granzscientific/pi-zero-geiger-counter/images/REV A/IMG_2127.JPG

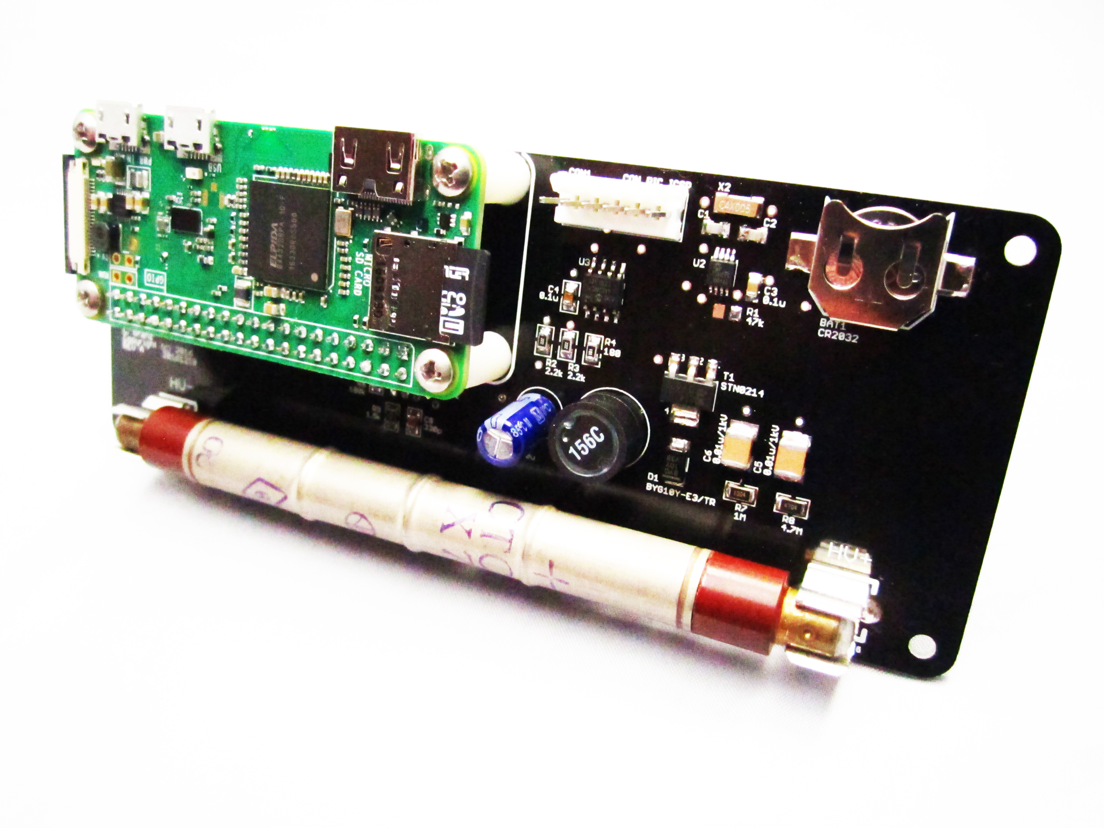
images/REV A/IMG_2127.JPG
