granzscientific/pi-zero-geiger-counter/images/REV A/IMG_2128.JPG

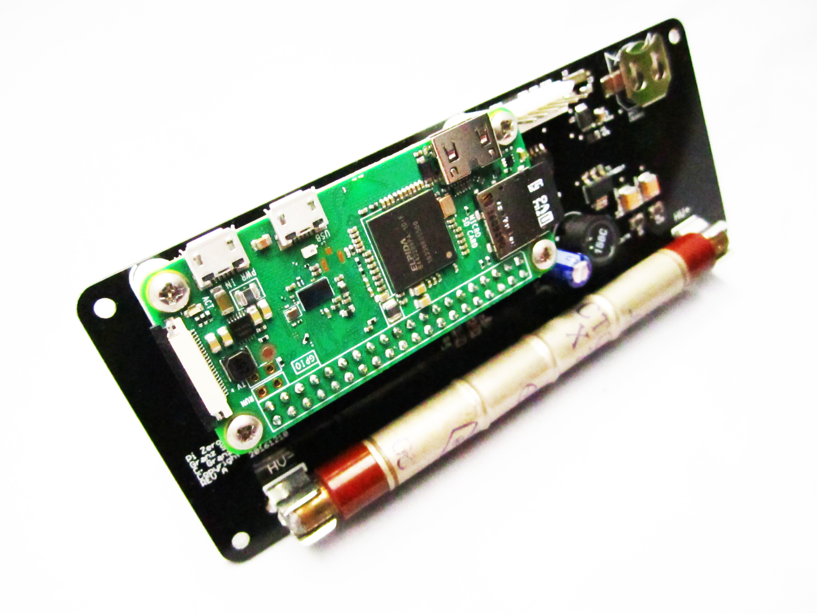
images/REV A/IMG_2128.JPG
