granzscientific/pi-zero-geiger-counter/images/REV A/IMG_2132.JPG

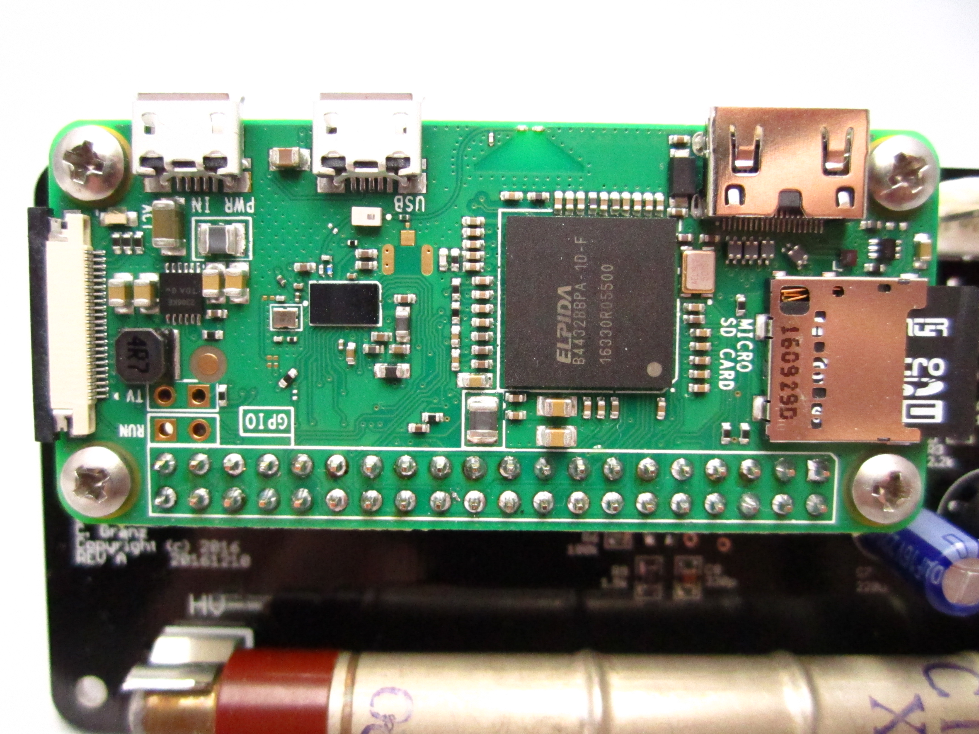
images/REV A/IMG_2132.JPG
