granzscientific/pi-zero-geiger-counter/pi-software/geiger_test.py

#!/usr/bin/env python

import sys
import time
import smbus
import RPi.GPIO as GPIO

i2c_addr = 0x19
gpio_pin = 7
total_count = 0

# I2C config for HV
bus = smbus.SMBus(1) # I2C1 port
bus.write_byte(i2c_addr, 0x71)

#GPIO.setmode(GPIO.BCM)
#GPIO.setup(gpio_pin, GPIO.IN, pull_up_down=GPIO.PUD_DOWN)
GPIO.setmode(GPIO.BOARD)
GPIO.setup(gpio_pin, GPIO.IN)

def my_callback(channel):
	global total_count
	total_count = total_count + 1
	sys.stdout.write('*')
	sys.stdout.flush()

GPIO.add_event_detect(gpio_pin, GPIO.FALLING)
GPIO.add_event_callback(gpio_pin, my_callback)

while True:
	raw_input('')
	print(str(total_count))
	#test = GPIO.input(gpio_pin)
	#print 'Got: ' + str(test)
